sparkfun/Decade_Resistance_Box/tutorial-images/43K.png

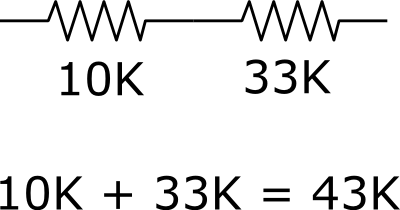
tutorial-images/43K.png
