sparkfun/Decade_Resistance_Box/tutorial-images/reading.png

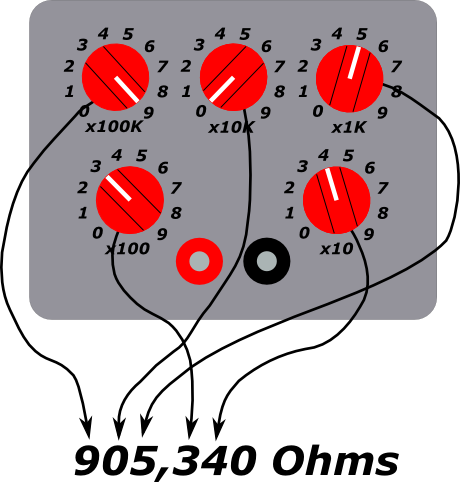
tutorial-images/reading.png
